JGAguado/Smart_Dashboard/Documentation/Silkscreen/Bottom.bmp

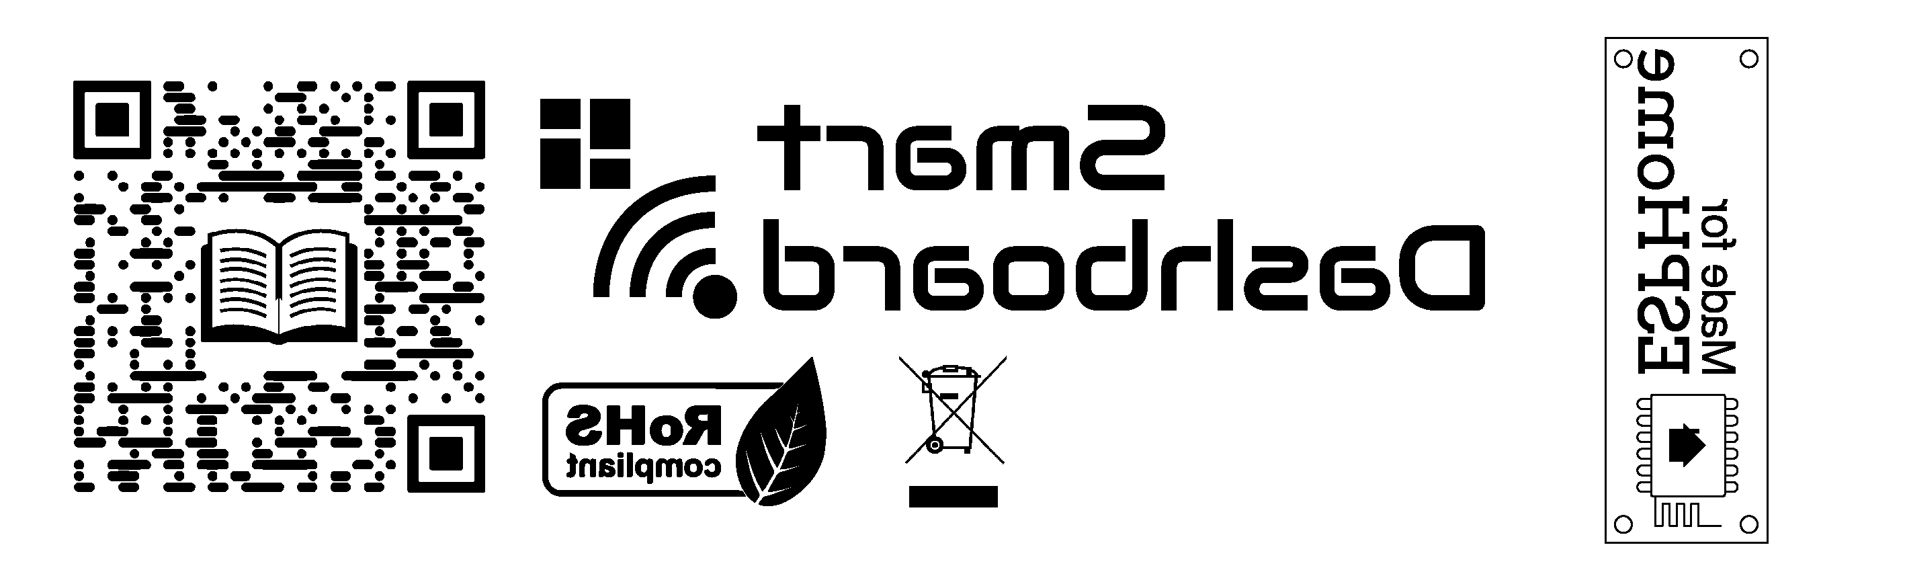
Documentation/Silkscreen/Bottom.bmp
