JGAguado/Smart_Dashboard/Documentation/Silkscreen/Top.bmp

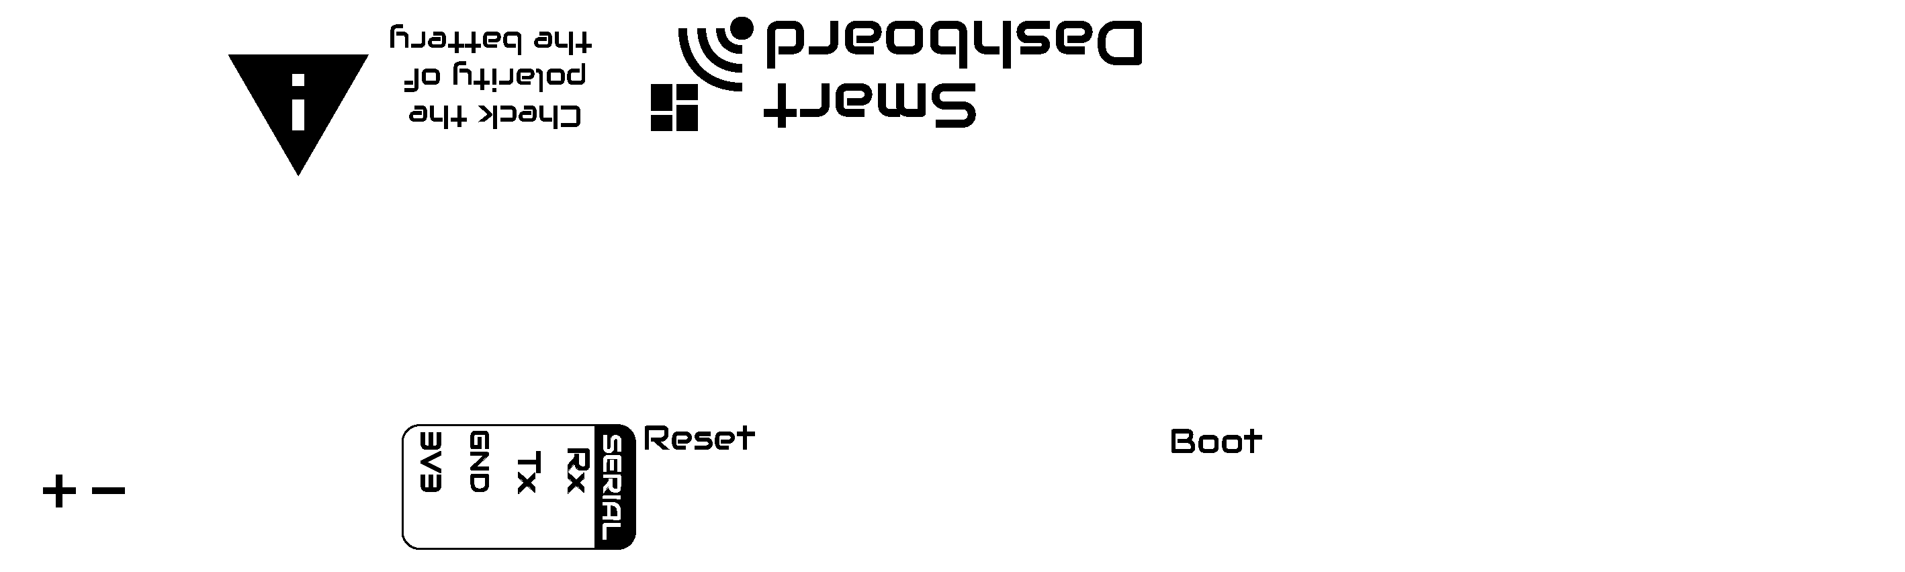
Documentation/Silkscreen/Top.bmp
